vuktacic/vdar/project/scans/2026-05-13_10-14-25.png

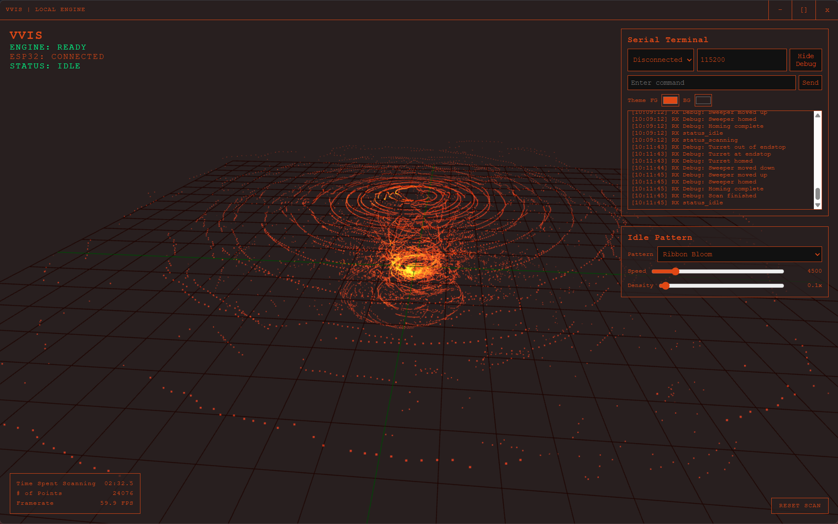
project/scans/2026-05-13_10-14-25.png
