vuktacic/vdar/project/scans/2026-05-13_11-41-44.png

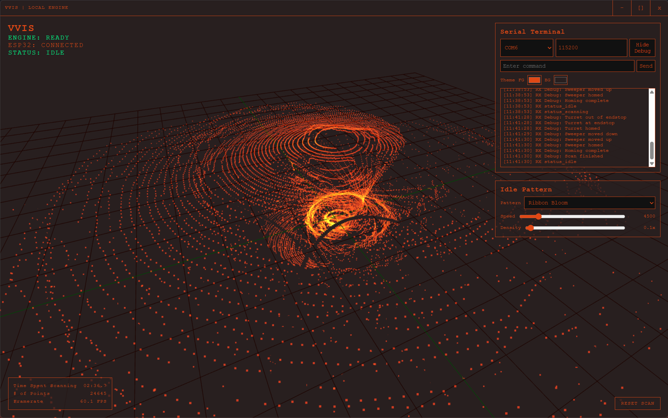
project/scans/2026-05-13_11-41-44.png
