vuktacic/vdar/project/scans/next.png

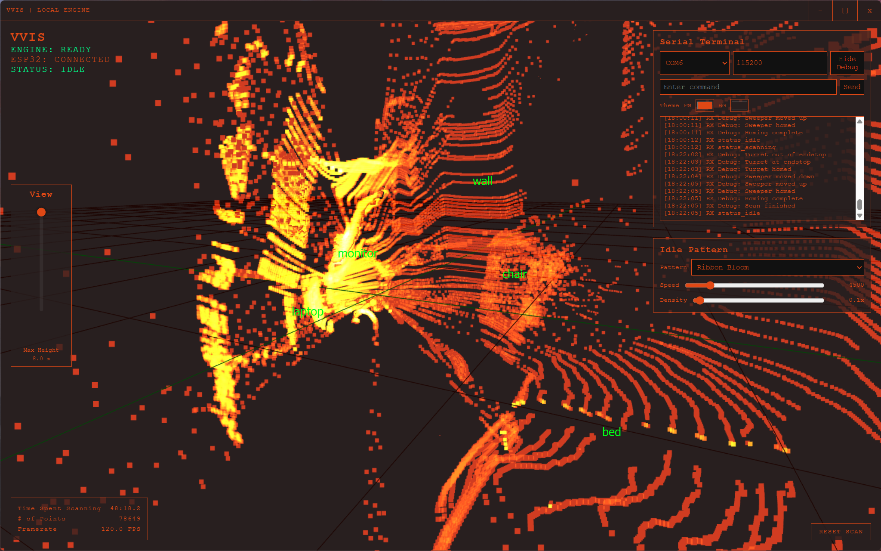
project/scans/next.png
